bogdan1775/TSC_EBookReader/Images/3-top.PNG

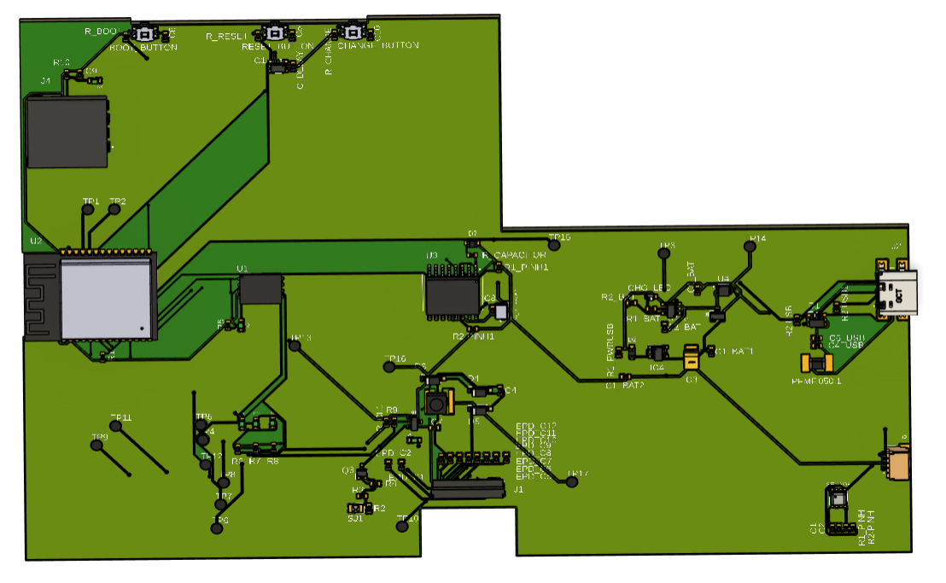
Images/3-top.PNG
