bogdan1775/TSC_EBookReader/Images/PCB-top-dupa_review.PNG

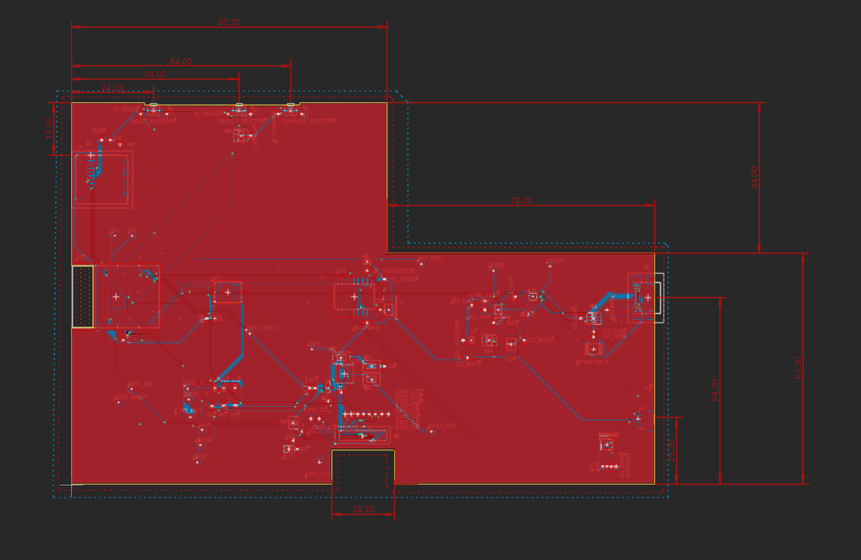
Images/PCB-top-dupa_review.PNG
