bogdan1775/TSC_EBookReader/Images/PCB-top.PNG

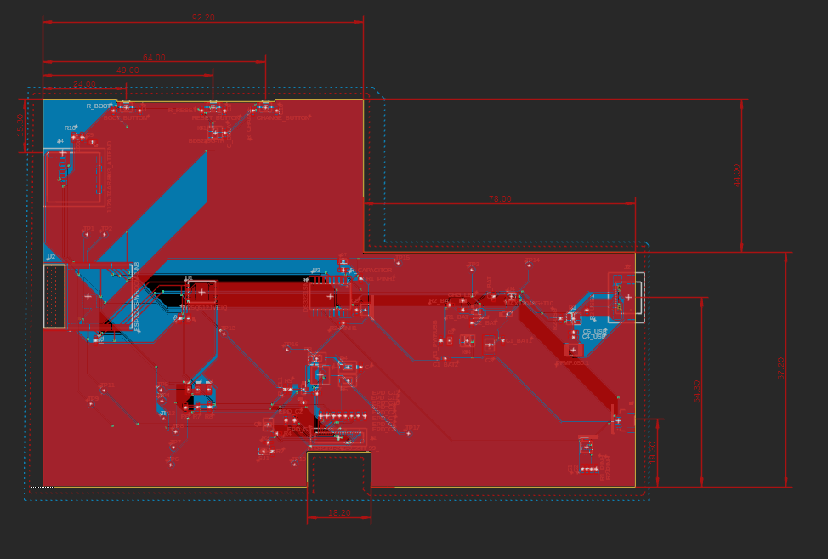
Images/PCB-top.PNG
